Milk-Cool/OpenVocakey/src/cvt.cpp

#include "cvt.h"
#include <map>

static int g_stretch = 25;
static std::map<String, String> prolong_map = {
    {"か", "あ"},
    {"が", "い"},
    {"き", "い"},
    {"ぎ", "い"},
    {"く", "う"},
    {"ぐ", "う"},
    {"け", "え"},
    {"げ", "え"},
    {"こ", "お"},
    {"ご", "お"},
    {"さ", "あ"},
    {"ざ", "あ"},
    {"し", "い"},
    {"じ", "い"},
    {"す", "う"},
    {"ず", "う"},
    {"せ", "え"},
    {"ぜ", "え"},
    {"そ", "お"},
    {"ぞ", "お"},
    {"た", "あ"},
    {"だ", "あ"},
    {"ち", "い"},
    {"つ", "う"},
    {"て", "え"},
    {"で", "え"},
    {"と", "お"},
    {"ど", "お"},
    {"な", "あ"},
    {"に", "い"},
    {"ぬ", "う"},
    {"ね", "え"},
    {"の", "お"},
    {"は", "あ"},
    {"ば", "あ"},
    {"ぱ", "あ"},
    {"ひ", "い"},
    {"び", "い"},
    {"ぴ", "い"},
    {"ふ", "う"},
    {"ぶ", "う"},
    {"ぷ", "う"},
    {"へ", "え"},
    {"べ", "え"},
    {"ぺ", "え"},
    {"ほ", "お"},
    {"ぼ", "お"},
    {"ぽ", "お"},
    {"ま", "あ"},
    {"み", "い"},
    {"む", "う"},
    {"め", "え"},
    {"も", "お"},
    {"や", "あ"},
    {"ゆ", "う"},
    {"よ", "お"},
    {"ら", "あ"},
    {"り", "い"},
    {"る", "う"},
    {"れ", "え"},
    {"ろ", "お"},
    {"わ", "あ"},
    {"を", "お"},
    {"あ", "あ"},
    {"い", "い"},
    {"う", "う"},
    {"え", "え"},
    {"お", "お"},
    {"いぇ", "え"},
    {"うぃ", "い"},
    {"うぇ", "え"},
    {"うぉ", "お"},
    {"カ", "あ"},
    {"ガ", "あ"},
    {"キ", "い"},
    {"ギ", "い"},
    {"きぇ", "え"},
    {"ぎぇ", "え"},
    {"きゃ", "あ"},
    {"ぎゃ", "あ"},
    {"きゅ", "う"},
    {"ぎゅ", "う"},
    {"きょ", "お"},
    {"ぎょ", "お"},
    {"ク", "う"},
    {"グ", "う"},
    {"ケ", "え"},
    {"ゲ", "え"},
    {"コ", "お"},
    {"ゴ", "お"},
    {"しぇ", "え"},
    {"じぇ", "え"},
    {"しゃ", "あ"},
    {"じゃ", "あ"},
    {"しゅ", "う"},
    {"じゅ", "う"},
    {"しょ", "お"},
    {"じょ", "お"},
    {"すぃ", "い"},
    {"ずぃ", "い"},
    {"ちぇ", "え"},
    {"ちゃ", "あ"},
    {"ちゅ", "う"},
    {"ちょ", "お"},
    {"つぁ", "あ"},
    {"つぃ", "い"},
    {"つぇ", "え"},
    {"つぉ", "お"},
    {"てぃ", "い"},
    {"でぃ", "い"},
    {"てゅ", "う"},
    {"でゅ", "う"},
    {"とぅ", "う"},
    {"どぅ", "う"},
    {"にぇ", "え"},
    {"にゃ", "あ"},
    {"にゅ", "う"},
    {"にょ", "お"},
    {"ひぇ", "え"},
    {"びぇ", "え"},
    {"ぴぇ", "え"},
    {"ひゃ", "あ"},
    {"びゃ", "あ"},
    {"ぴゃ", "あ"},
    {"ひゅ", "う"},
    {"びゅ", "う"},
    {"ぴゅ", "う"},
    {"ひょ", "お"},
    {"びょ", "お"},
    {"ぴょ", "お"},
    {"ふぁ", "あ"},
    {"ふぃ", "い"},
    {"ふぇ", "え"},
    {"ふぉ", "お"},
    {"みぇ", "え"},
    {"みゃ", "あ"},
    {"みゅ", "う"},
    {"みょ", "お"},
    {"りぇ", "え"},
    {"りゃ", "あ"},
    {"りゅ", "う"},
    {"りょ", "お"},
    {"ん", "ん"},
    {"ア", "ア"},
    {"イ", "イ"},
    {"ウ", "ウ"},
    {"エ", "エ"},
    {"オ", "オ"},
    {"カ", "ア"},
    {"キ", "イ"},
    {"ク", "ウ"},
    {"ケ", "エ"},
    {"コ", "オ"},
    {"キャ", "ア"},
    {"キュ", "ウ"},
    {"キョ", "オ"},
    {"ガ", "ア"},
    {"ギ", "イ"},
    {"グ", "ウ"},
    {"ゲ", "エ"},
    {"ゴ", "オ"},
    {"ギャ", "ア"},
    {"ギュ", "ウ"},
    {"ギョ", "オ"},
    {"サ", "ア"},
    {"シ", "イ"},
    {"ス", "ウ"},
    {"セ", "エ"},
    {"ソ", "オ"},
    {"シャ", "ア"},
    {"シュ", "ウ"},
    {"ショ", "オ"},
    {"ザ", "ア"},
    {"ジ", "イ"},
    {"ズ", "ウ"},
    {"ゼ", "エ"},
    {"ゾ", "オ"},
    {"ジャ", "ア"},
    {"ジュ", "ウ"},
    {"ジョ", "オ"},
    {"タ", "ア"},
    {"チ", "イ"},
    {"ツ", "ウ"},
    {"テ", "エ"},
    {"ト", "オ"},
    {"チャ", "ア"},
    {"チュ", "ウ"},
    {"チョ", "オ"},
    {"ダ", "ア"},
    {"ヂ", "イ"},
    {"ヅ", "ウ"},
    {"デ", "エ"},
    {"ド", "オ"},
    {"ヂャ", "ア"},
    {"ヂュ", "ウ"},
    {"ヂョ", "オ"},
    {"ナ", "ア"},
    {"ニ", "イ"},
    {"ヌ", "ウ"},
    {"ネ", "エ"},
    {"ノ", "オ"},
    {"ニャ", "ア"},
    {"ニュ", "ウ"},
    {"ニョ", "オ"},
    {"ハ", "ア"},
    {"ヒ", "イ"},
    {"フ", "ウ"},
    {"ヘ", "エ"},
    {"ホ", "オ"},
    {"ヒャ", "ア"},
    {"ヒュ", "ウ"},
    {"ヒョ", "オ"},
    {"バ", "ア"},
    {"ビ", "イ"},
    {"ブ", "ウ"},
    {"ベ", "エ"},
    {"ボ", "オ"},
    {"ビャ", "ア"},
    {"ビュ", "ウ"},
    {"ビョ", "オ"},
    {"パ", "ア"},
    {"ピ", "イ"},
    {"プ", "ウ"},
    {"ペ", "エ"},
    {"ポ", "オ"},
    {"ピャ", "ア"},
    {"ピュ", "ウ"},
    {"ピョ", "オ"},
    {"マ", "ア"},
    {"ミ", "イ"},
    {"ム", "ウ"},
    {"メ", "エ"},
    {"モ", "オ"},
    {"ミャ", "ア"},
    {"ミュ", "ウ"},
    {"ミョ", "オ"},
    {"ヤ", "ア"},
    {"ユ", "ウ"},
    {"ヨ", "オ"},
    {"ラ", "ア"},
    {"リ", "イ"},
    {"ル", "ウ"},
    {"レ", "エ"},
    {"ロ", "オ"},
    {"リャ", "ア"},
    {"リュ", "ウ"},
    {"リョ", "オ"},
    {"ワ", "ア"},
    {"ヰ", "イ"},
    {"ヱ", "エ"},
    {"ヲ", "オ"},
    {"ン", "ン"},
};

String cvt_syl(String& syl) {
    if(!prolong_map.contains(syl)) return syl;
    String o = syl;
    for(int i = 0; i < g_stretch; i++)
        o += prolong_map[syl];
    return o;
}
void set_stretch(int stretch) {
    g_stretch = stretch;
}
int get_stretch() {
    return g_stretch;
}
